ultralyj/merci/Models/press_ indenter.SLDPRT

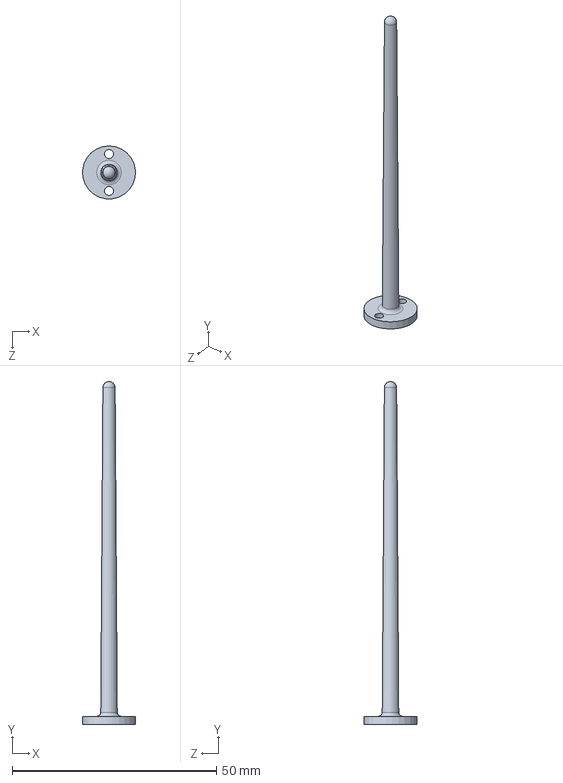
[picture p24: CAD file, 2023-03-09]
Models/press_ indenter.SLDPRT
13.0 x 83.9 x 13.0 mm
