ultralyj/merci/Models/merci_middle_1.4.SLDPRT

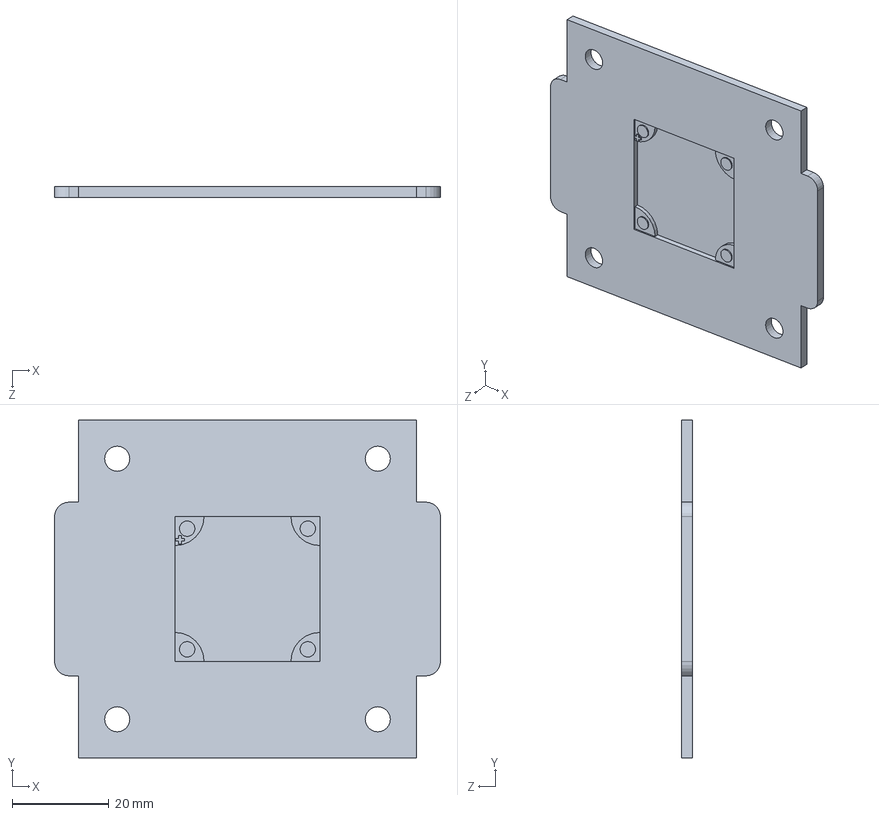
[picture p25: CAD file, 2023-03-09]
Models/merci_middle_1.4.SLDPRT
80.0 x 70.0 x 2.20 mm
