ultralyj/merci/Models/merci_top.SLDPRT

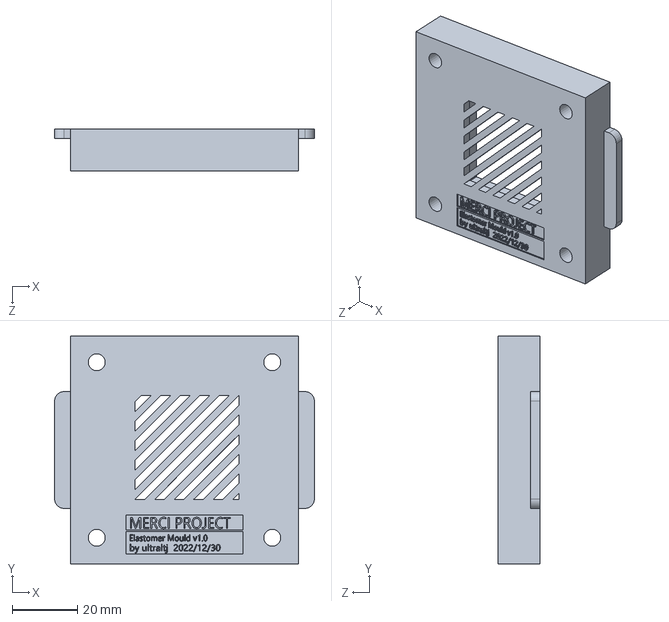
[picture p26: CAD file, 2023-03-09]
Models/merci_top.SLDPRT
80.0 x 70.0 x 13.0 mm
