ultralyj/merci/Models/magcube_10mm.SLDPRT

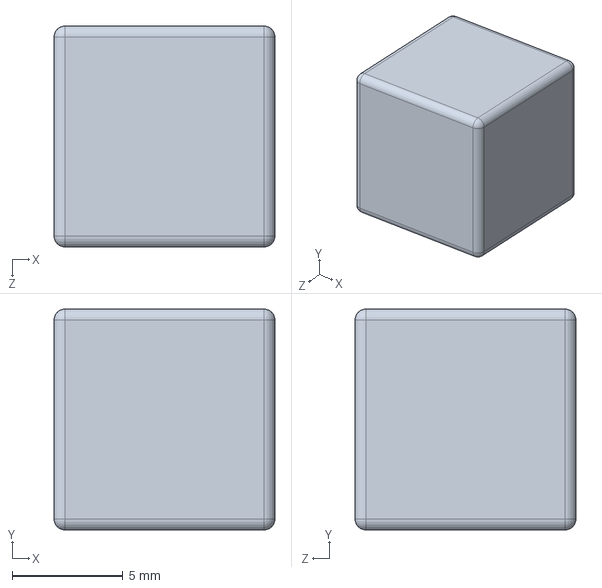
[picture p27: CAD file, 2023-03-09]
Models/magcube_10mm.SLDPRT
10.0 x 10.0 x 10.0 mm
