ultralyj/merci/Models/merci_bottom.SLDPRT

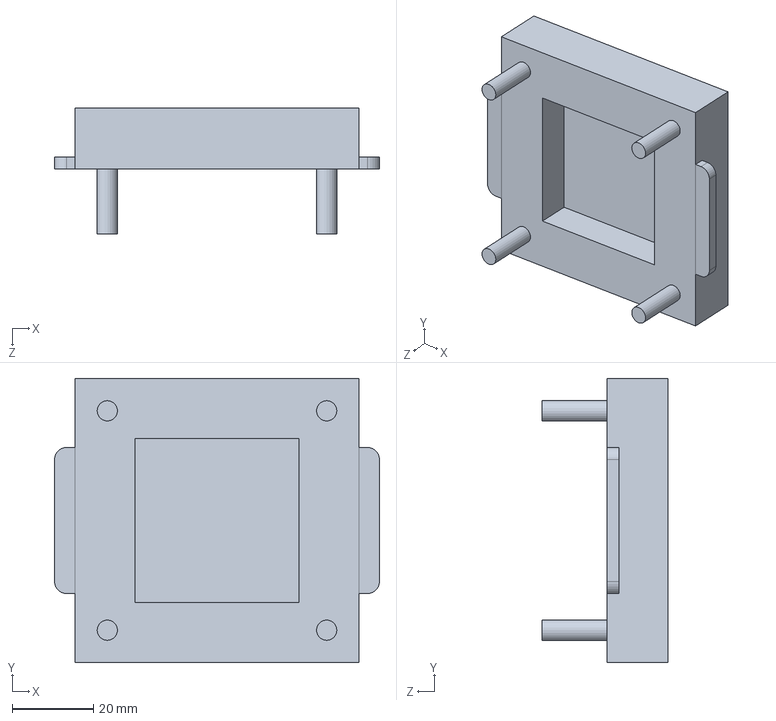
[picture p28: CAD file, 2023-03-09]
Models/merci_bottom.SLDPRT
80.0 x 70.0 x 31.0 mm
