ultralyj/merci/Models/merci_middle_2.3.SLDPRT

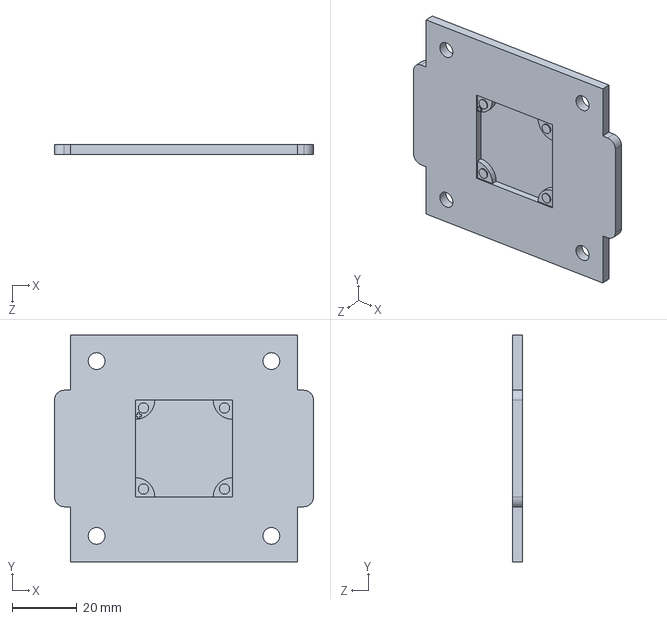
[picture p29: CAD file, 2023-03-09]
Models/merci_middle_2.3.SLDPRT
80.0 x 70.0 x 3.10 mm
