ultralyj/merci/Models/press_outer.SLDPRT

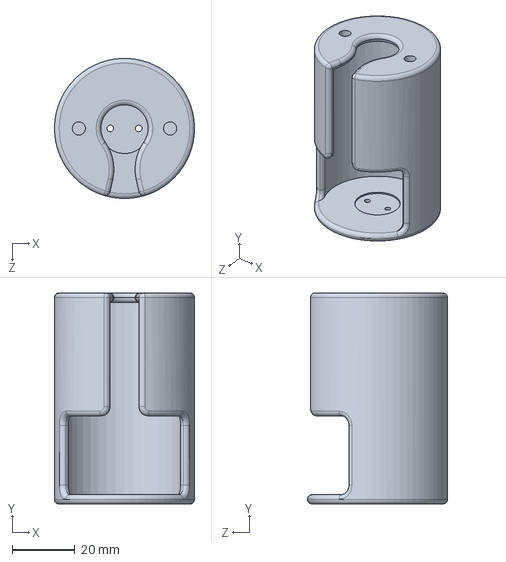
[picture p30: CAD file, 2023-03-09]
Models/press_outer.SLDPRT
44.5 x 67.0 x 44.5 mm
