ultralyj/merci/Models/merci_middle.SLDPRT

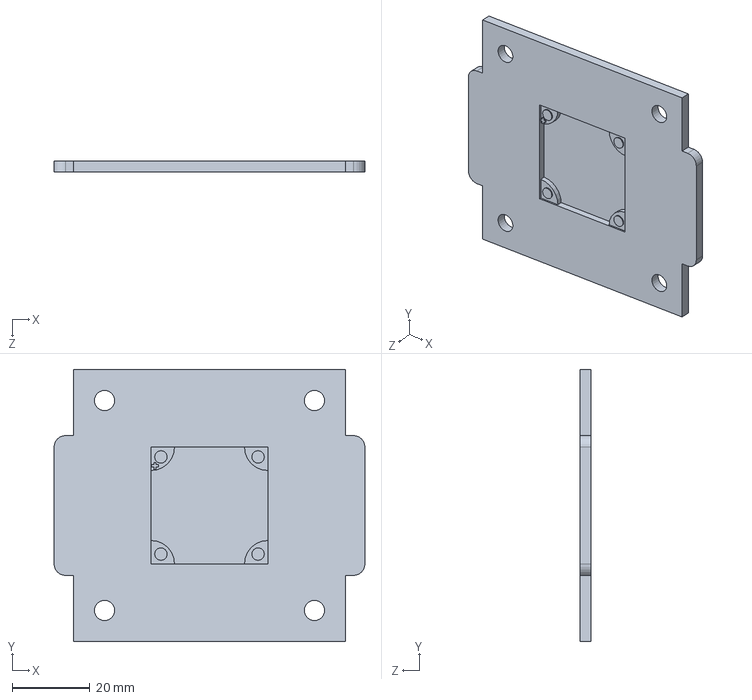
[picture p31: CAD file, 2023-03-09]
Models/merci_middle.SLDPRT
80.0 x 70.0 x 2.80 mm
