ultralyj/merci/Models/press_sensor.SLDPRT

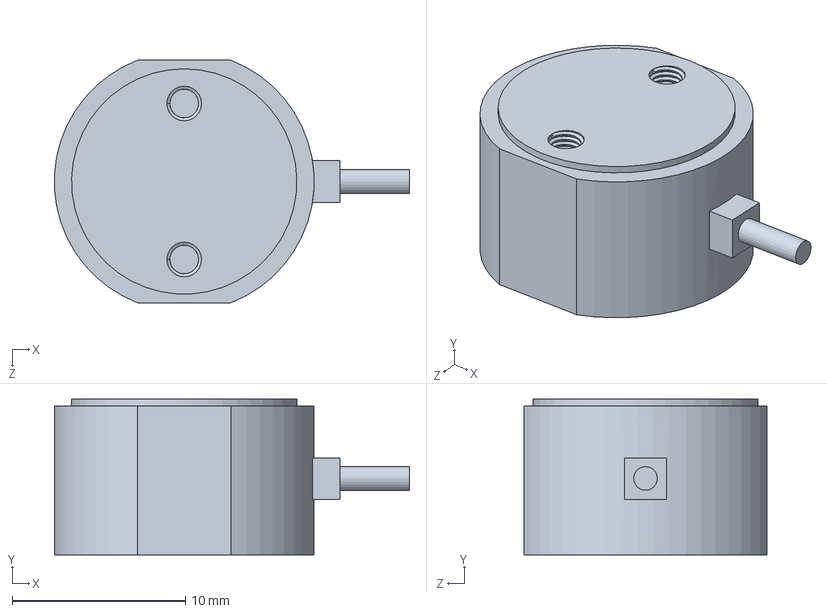
[picture p32: CAD file, 2023-03-09]
Models/press_sensor.SLDPRT
20.5 x 9.00 x 14.0 mm
