ultralyj/merci/Calibration/sidebar.bmp

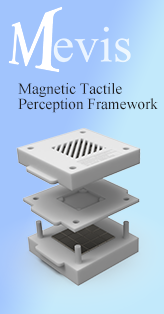
Calibration/sidebar.bmp
