ultralyj/merci/Bsp/mnode_f4/X-CUBE-AI/App/network_data_params.c

/**
  ******************************************************************************
  * @file    network_data_params.c
  * @author  AST Embedded Analytics Research Platform
  * @date    Fri May 19 21:38:22 2023
  * @brief   AI Tool Automatic Code Generator for Embedded NN computing
  ******************************************************************************
  * Copyright (c) 2023 STMicroelectronics.
  * All rights reserved.
  *
  * This software is licensed under terms that can be found in the LICENSE file
  * in the root directory of this software component.
  * If no LICENSE file comes with this software, it is provided AS-IS.
  ******************************************************************************
  */

#include "network_data_params.h"


/**  Activations Section  ****************************************************/
ai_handle g_network_activations_table[1 + 2] = {
  AI_HANDLE_PTR(AI_MAGIC_MARKER),
  AI_HANDLE_PTR(NULL),
  AI_HANDLE_PTR(AI_MAGIC_MARKER),
};




/**  Weights Section  ********************************************************/
AI_ALIGNED(32)
const ai_u64 s_network_weights_array_u64[5313] = {
  0x3e317b7fbe242275U, 0xbdb65b81be2178a8U, 0xbbd85aa6bb8f66eaU, 0xbe769afcbd20b337U,
  0xbe5161fbbe357754U, 0xbb7d524bbd031709U, 0x3ce84cfabe53f8feU, 0xbda7bddc3e4b8bafU,
  0x3e44cd1c3df61047U, 0xbe545b9cbe47674aU, 0x3d37fdea3d02f05cU, 0xbd7112a0bd13d87dU,
  0xbe12ee45bd4290ebU, 0xbddafd45bdb97eacU, 0x3e30a340be4d5e94U, 0xbe783ea4bd6f8e46U,
  0xbd11800c3e316148U, 0x3d15e1aabddfc0acU, 0xbe3a8ce53e261916U, 0x3c78ef54be492013U,
  0xbc64f6413c4bdb41U, 0x3e42db943e669e2eU, 0xbde3ca7a3d33168bU, 0x3e37d0b2bdef92b4U,
  0x3e27d023be0c3689U, 0x3e1359adbe479943U, 0xbe0dc8c8be4bda30U, 0xbe2e8cedbda2d6e2U,
  0xbe43f5bdbe02d095U, 0x3e3ed72b3e5ce28eU, 0xbdf6be7cbca33a4cU, 0xbde0d2723d43c8c0U,
  0x3d2613a73e3ca4a8U, 0xbf08caa3bc51e736U, 0xbf3693cc3f593e54U, 0x3dbfe4b4bf559836U,
  0x3eb27ff7bd03e341U, 0x3f41d72cbf46f226U, 0x3f3bfa233d69854aU, 0xbf357a6a3d87e5c0U,
  0xbc122f9f3e95103fU, 0x3e1d060c3ef7a329U, 0x3f4e28123f37ba7aU, 0x3f5a6e46bf40dba2U,
  0x3ee7ab523f493de0U, 0x3f35c1293f357e19U, 0xbef7478b3e0d5df3U, 0x3e41b2693f571633U,
  0x3f5492813d387718U, 0x3f603e353f215854U, 0x3e24b7553daa0214U, 0xbf550a1d3d9c3209U,
  0x3f5494a83f4b5ffeU, 0xbe1575d3be8e87dcU, 0x3f30ac21bf4b8e13U, 0xbe3137923f313e35U,
  0x3e12c88e3f23f0f0U, 0xbee902be3ea497e0U, 0x3f3af6113ead0e5bU, 0x3edf3f853f5a0040U,
  0x3db6677e3f328397U, 0xbec72754be9558f8U, 0xbe69f66b3f4bffb7U, 0x3f499dd93f477bb8U,
  0xbf10527b3f174107U, 0x3f2cbd5d3f1ee2c0U, 0x3ec688bfbec20abdU, 0x3f0d75f83f247ffeU,
  0x3ee2a0d03f235876U, 0xbedf89993f2eece8U, 0xbede5c3c3f0abce1U, 0x3f1a4580bf11d663U,
  0xbf092a99bf180e7bU, 0x3f124f213ed17715U, 0xbf071c48bf0f8f16U, 0xbdf6ac9f3ebcd424U,
  0x3ed9de9dbe8ea139U, 0x3eba4ac33d16f709U, 0xbeee840e3f03f388U, 0x3ee404d3bdea3721U,
  0xbbb8e379bf262227U, 0xbf2763753e4adfd4U, 0x3f09d910bf1d5b4fU, 0x3ec71aba3f0b16c3U,
  0xbee7f1d5be8f6a72U, 0xbf03b95dbed4c8b7U, 0x3e9996713e554ae3U, 0xbf0d22353e6981a8U,
  0xbf2443ad3e7a1cfeU, 0xbeec0df93ebf405aU, 0x3e91a82b3edcd6a7U, 0x3f0f83ffbdaffde1U,
  0x3eff3cc7bb597d7eU, 0xbebdc2dbbef470c3U, 0x3f30b2bdbe7ce9c6U, 0x3e420ddfbf332060U,
  0x4118dbe44111517cU, 0xbe2b51e6bde0af26U, 0xbe61f13bbe325d08U, 0xbdbc3f9cbe34a4b4U,
  0xbe2c2d3fbb49af80U, 0x3d8bf633bd89c60cU, 0xbf03d2743f1253bbU, 0xbdf24f66bdcf8f74U,
  0xbf2d331abdea325cU, 0x3db9e0093ef3cd65U, 0xbda1fd493f12e4fbU, 0xbd3aaf143e4a2e1aU,
  0xbe384195bbbeed20U, 0x3e8fb9373dda274eU, 0x3e76086dbf24aa93U, 0x3e6c59c6be95e87fU,
  0x3f26d4b7be6038ccU, 0x3d0f9e543d1fbfc5U, 0xbef1101b3e3219e8U, 0xbefad8fe3e77c6c5U,
  0xbe6144313e57b6e6U, 0x3d21b2d0bded9a3fU, 0xbf2ab8753e1d1a16U, 0xbe0c41f93db21e09U,
  0xbde93140bd0f69e4U, 0x3e434c36bcbfce2bU, 0x3ec71c4b3ed9c626U, 0x3e2f89cfbf27879bU,
  0xbf55dd7d3e62691cU, 0xbf6c5c443dafe294U, 0x3f079ac83cdb2a97U, 0x3e2271a03ea8d8a0U,
  0xbe43f4273e64f4afU, 0x3cea6d80be33ebb2U, 0x3ec27dd23cc38247U, 0x3ee4b645bf1b9ca6U,
  0x3e06b06c3e65dd08U, 0x3d64bf323dafeab2U, 0x3e23a2e8bfaf330bU, 0x3e6359d73ec1413dU,
  0xbe77b0d93aed12aaU, 0x3ef2f0313f2bc1faU, 0xbe8ecbdb3eaca529U, 0xbf118fea3ed0f1beU,
  0x3f1677303e4747faU, 0xbda1d6e0bd67c18aU, 0xbe1a3e163cee6d80U, 0xbd94ee9abe5920e6U,
  0xbe6b18e0bdf03ad8U, 0x0U, 0xbe24787900000000U, 0xbe5145ab00000000U,
  0xbe72d62cU, 0xbe12f89e3d8eb0f5U, 0x3bfa915cbdc16155U, 0xbbc4a7bcbd9f1194U,
  0x3decb09dU, 0xbe09f14ebe9cb658U, 0x3c1b32283d92bd1cU, 0xbe9f0ae2U,
  0xbe9e937cbc2e9d2dU, 0xbeaf07753e84374bU, 0xbe896ae2bd960814U, 0xbdcc099fbe5027d9U,
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
};


ai_handle g_network_weights_table[1 + 2] = {
  AI_HANDLE_PTR(AI_MAGIC_MARKER),
  AI_HANDLE_PTR(s_network_weights_array_u64),
  AI_HANDLE_PTR(AI_MAGIC_MARKER),
};
