ultralyj/merci/Bsp/mnode_f4/Core/Src/tickus.c

#include "tickus.h"

__STATIC_INLINE uint32_t LL_SYSTICK_IsActiveCounterFlag(void)
{
  return ((SysTick->CTRL & SysTick_CTRL_COUNTFLAG_Msk) == (SysTick_CTRL_COUNTFLAG_Msk));
}

uint32_t getCurrentMicros(void)
{
	/* Ensure COUNTFLAG is reset by reading SysTick control and status register */
	LL_SYSTICK_IsActiveCounterFlag();           
	uint32_t m = HAL_GetTick();
	const uint32_t tms = SysTick->LOAD + 1;
	__IO uint32_t u = tms - SysTick->VAL;
	if (LL_SYSTICK_IsActiveCounterFlag()) 
	{
		m = HAL_GetTick();
		u = tms - SysTick->VAL;
	}
	return (m * 1000 + (u * 1000) / tms);
}
