ultralyj/merci/Bsp/mnode_f4/Core/Src/test_data.c

/**
 * @file test_data.c
 * @author Luo-Yijie (1951578@tongji.edu.cn)
 * @brief keras model test data
 * @version 0.2
 * @date 2023-5-20
 *
 * @copyright Copyright (c) 2022
 *
 */
 
const float test_in[100][12]={
{0.08554305886216218,0.7571820598576451,0.24727150612861704,0.8342677073027738,0.13923786323299114,0.8915728367164064,0.31414079311404874,0.2189631913663519,0.9066918812051405,0.1922121940645567,0.15564968125615009,0.9354507193892536},
{0.22818323618750513,0.2531086527742046,0.8229697207141657,0.45626763401854087,0.17650948320863047,0.8510149218841316,0.3664309867814326,0.14002698015031806,0.9605449778656466,0.10085523982185784,0.21961237325118743,0.8791719682881474},
{0.2941876693210739,0.20684332390018012,0.7842950691218449,0.5145652412883368,0.1450147903253871,0.8751704523317878,0.3588994774054719,0.1825014453651957,0.8764344350367473,0.3086351633626293,0.11256578102939274,0.8599393168248997},
{0.2410721615630902,0.28612468913472244,0.7723176806402865,0.45700047634751373,0.17661388550548107,0.8912221919195857,0.3231786043652012,0.1971863557525535,0.9213048523660121,0.12974421629290966,0.23561374235228705,0.8616032103357152},
{0.33076102126262197,0.1687676871623358,0.7567582694352721,0.5985489721886336,0.16109274404036888,0.8215217984182026,0.3786351060559485,0.20439391019464243,0.8732969441698544,0.34284475623694466,0.04928763958413529,0.8728589605559363},
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
{ 10.931069 , 13.101692 },
{ 16.84974 , 16.744589 },
{ 16.324232 , 16.541828 },
{ 2.2951708 , 5.1183004 },
{ 12.558064 , 3.5336752 },
{ 2.610128 , 3.8746653 },
{ 17.013224 , 3.3809786 },
{ 4.586338 , 16.039375 },
{ 15.855464 , 3.2342968 },
{ 17.80482 , 2.0563316 },
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

};
